brisfknibis/ibis-trackers/Images/drift compensation.png

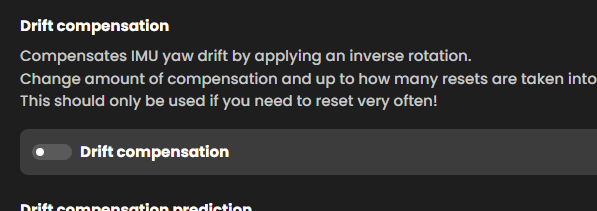
Images/drift compensation.png
