brisfknibis/ibis-trackers/Images/IbisTracker.jpg

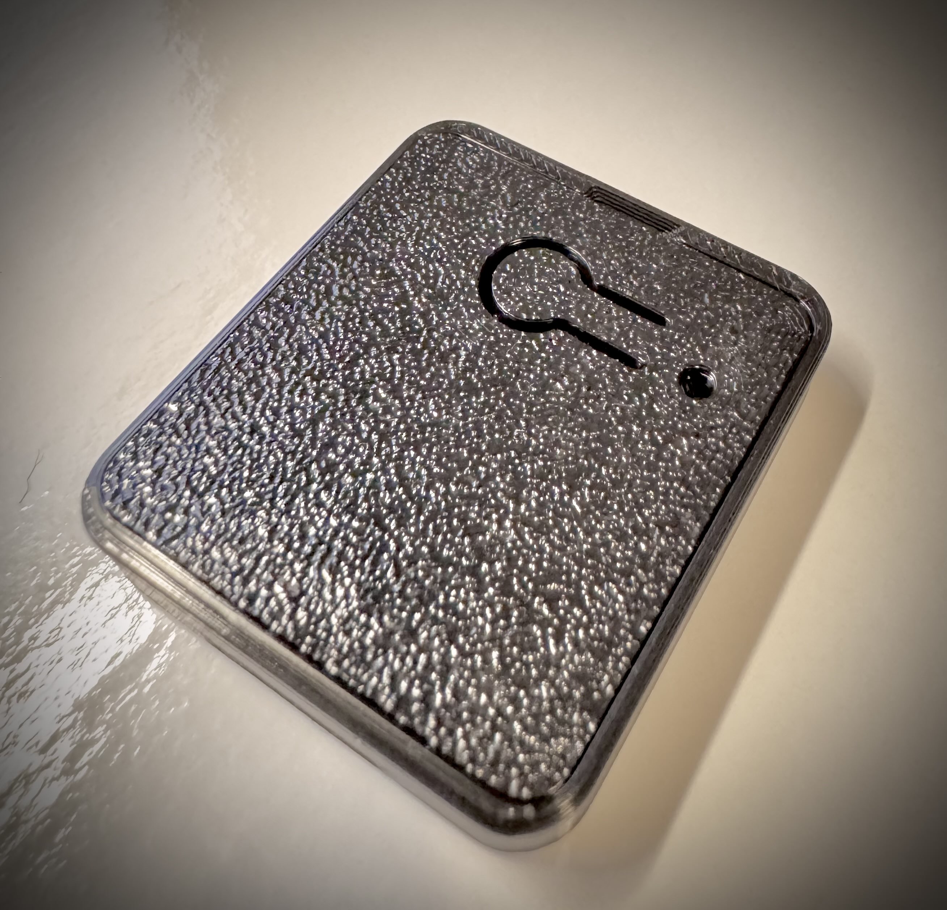
Images/IbisTracker.jpg
