brisfknibis/ibis-trackers/Images/image.png

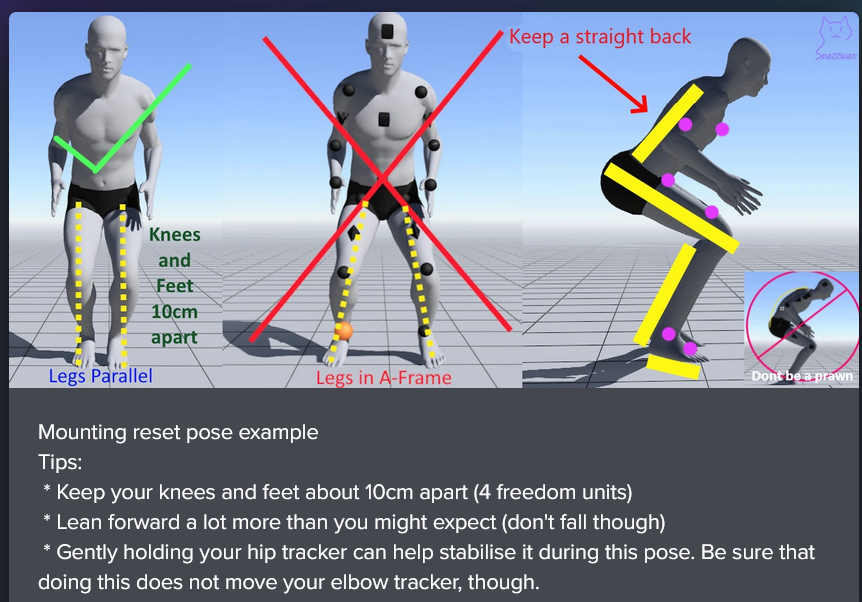
Images/image.png
