brisfknibis/ibis-trackers/Images/IMG_1489.png

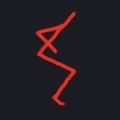
Images/IMG_1489.png
