brisfknibis/ibis-trackers/Images/IMG_7383.png

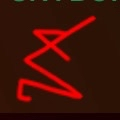
Images/IMG_7383.png
