brisfknibis/ibis-trackers/Images/process/31-mm-wire-antenna.jpg

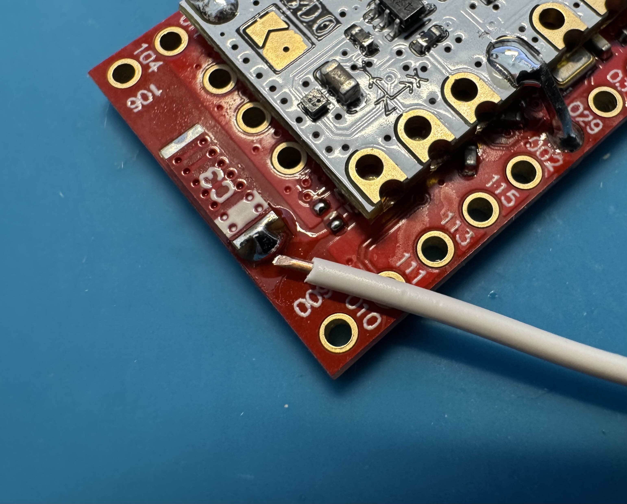
Images/process/31-mm-wire-antenna.jpg
