brisfknibis/ibis-trackers/Images/process/31mm-wire-2.jpg

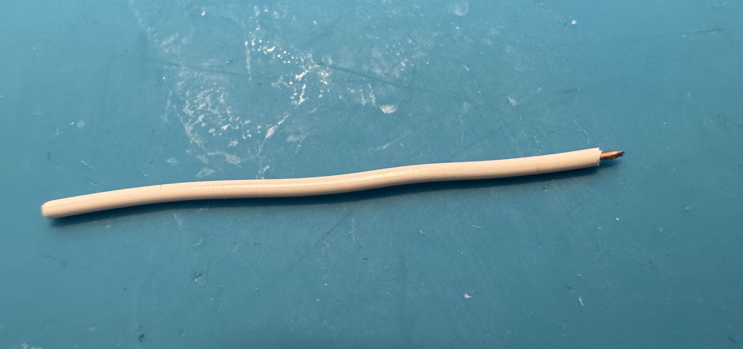
Images/process/31mm-wire-2.jpg
