brisfknibis/ibis-trackers/Images/process/31mm-wire.jpg

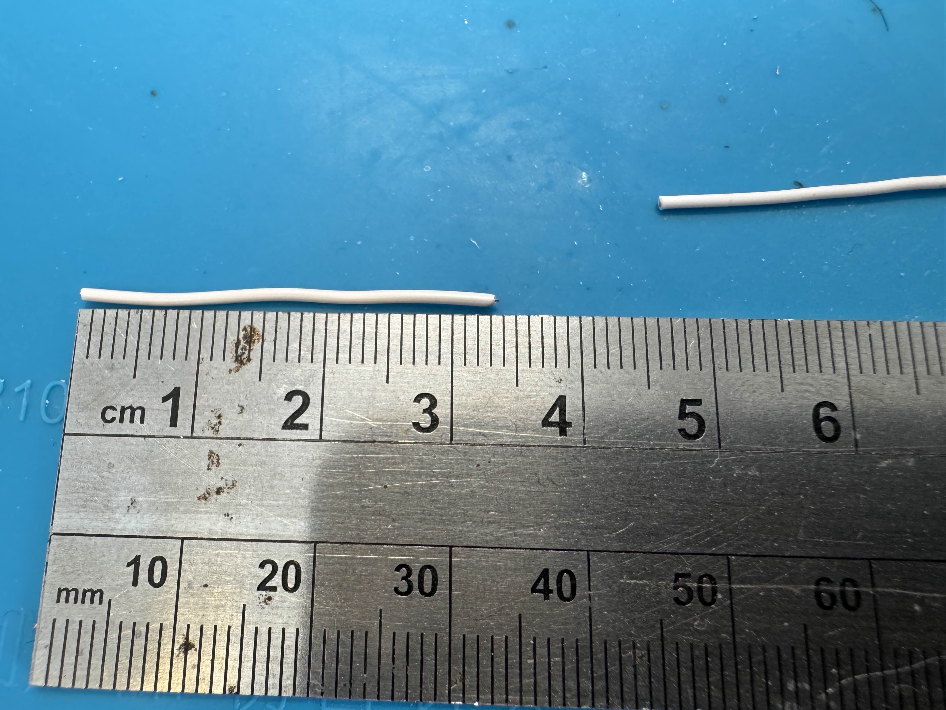
Images/process/31mm-wire.jpg
