brisfknibis/ibis-trackers/Images/process/battery-placement.jpg

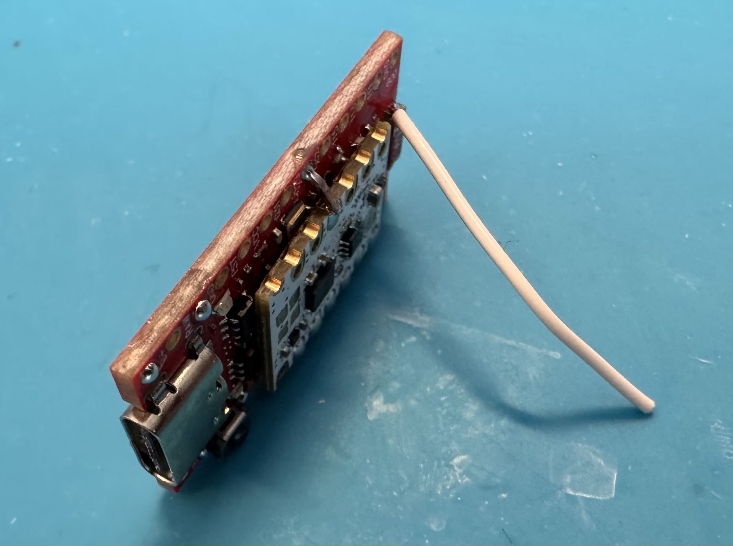
Images/process/battery-placement.jpg
