brisfknibis/ibis-trackers/Images/process/completed-tracker.jpg

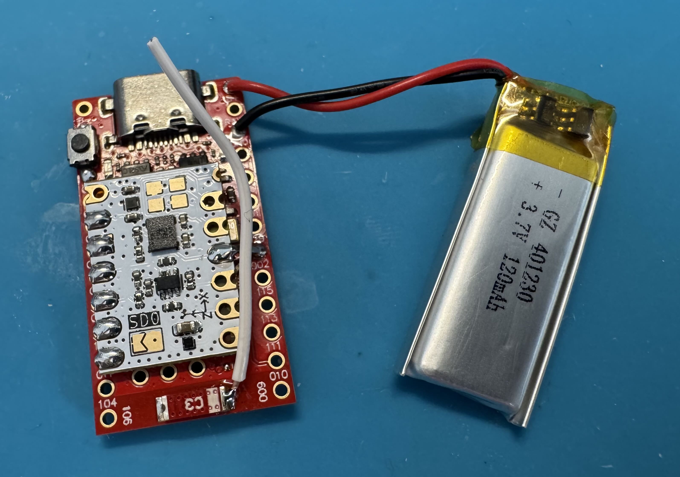
Images/process/completed-tracker.jpg
