brisfknibis/ibis-trackers/Images/process/imu-cube.jpg

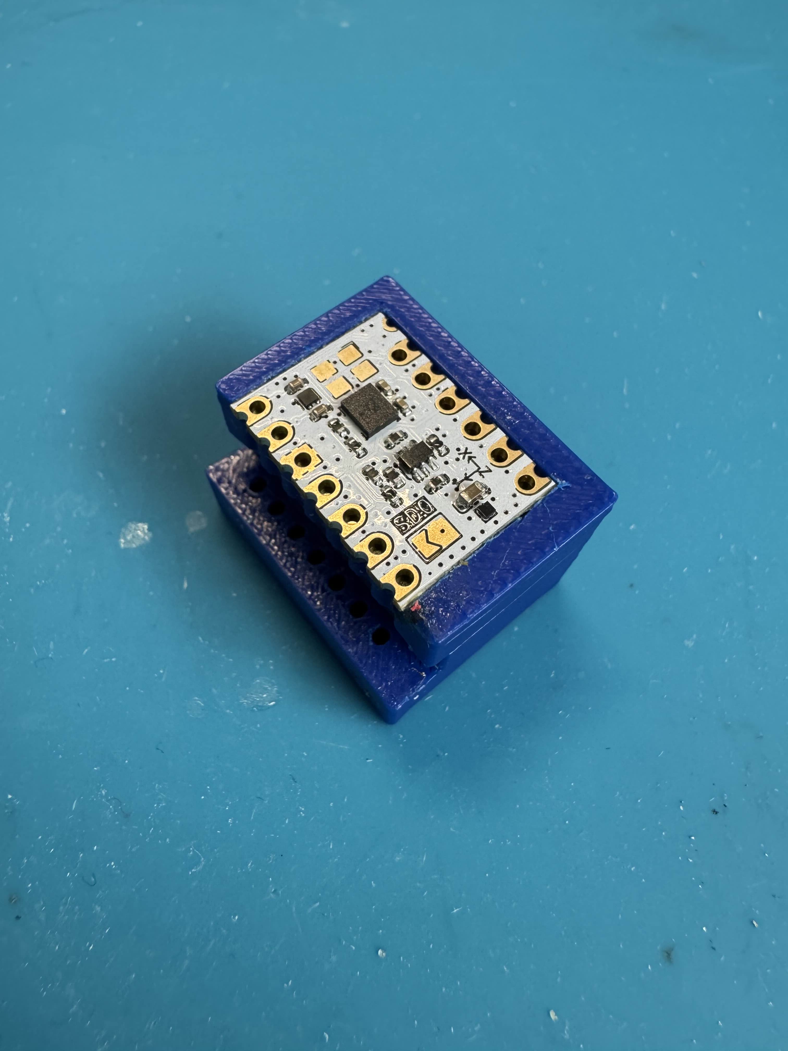
Images/process/imu-cube.jpg
