brisfknibis/ibis-trackers/Images/process/imu-pre-prep.jpg

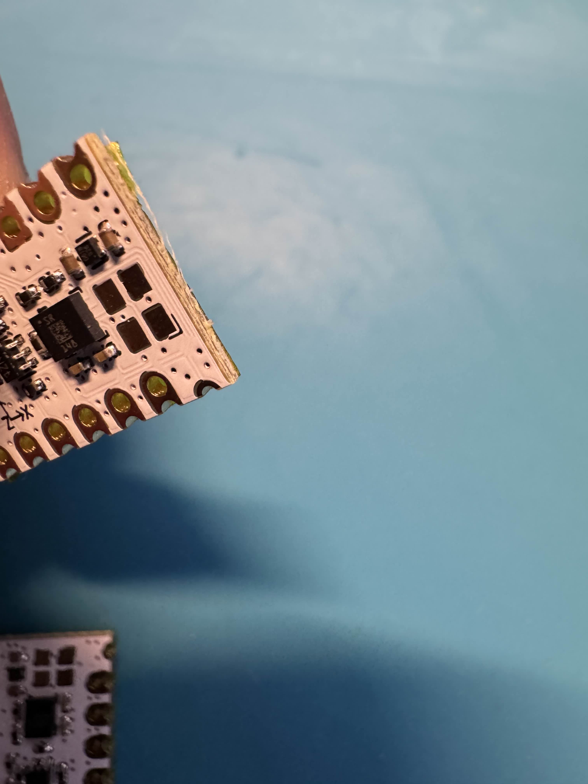
Images/process/imu-pre-prep.jpg
