brisfknibis/ibis-trackers/Images/process/imus-back.jpg

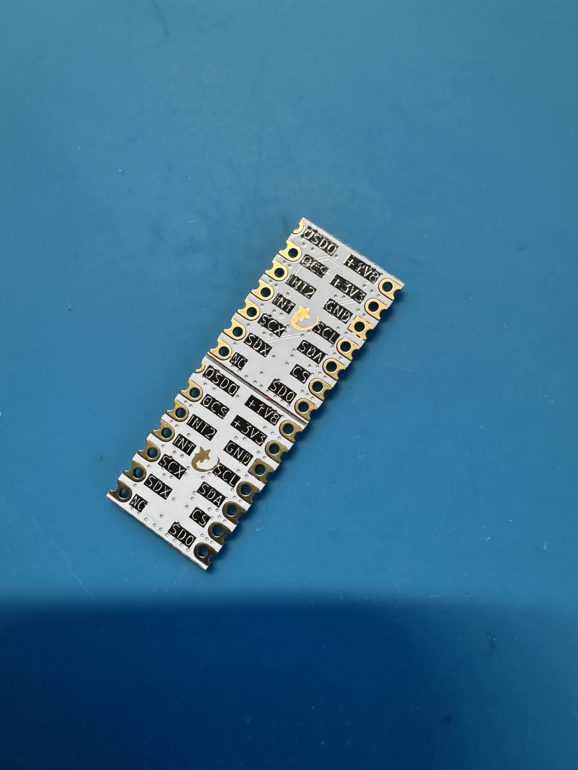
Images/process/imus-back.jpg
