brisfknibis/ibis-trackers/Images/process/imus-front.jpg

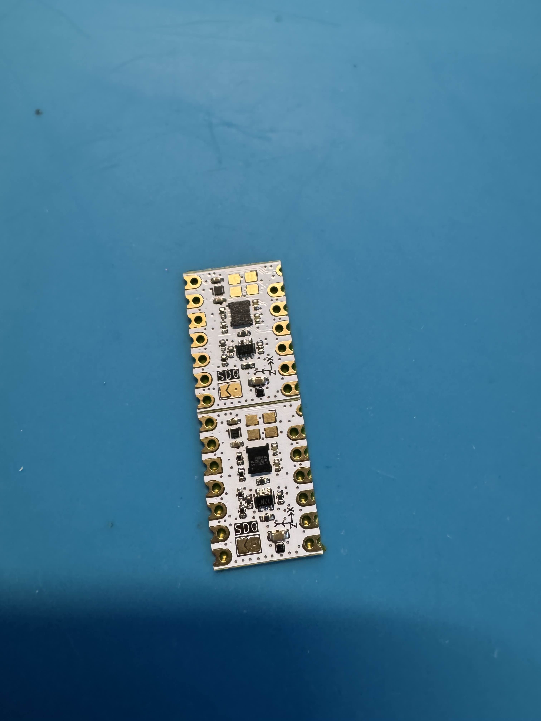
Images/process/imus-front.jpg
