brisfknibis/ibis-trackers/Images/process/serial-termainl-slimenrf-tracker.png

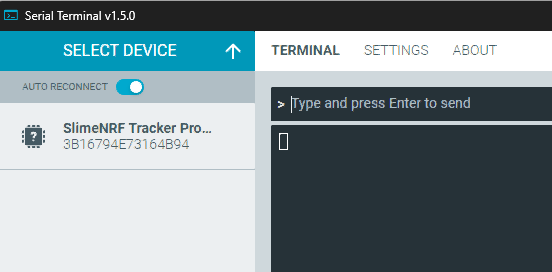
Images/process/serial-termainl-slimenrf-tracker.png
