brisfknibis/ibis-trackers/Images/process/serial-terminal-connect.png

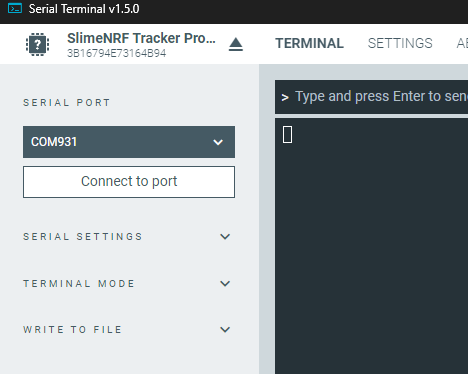
Images/process/serial-terminal-connect.png
