brisfknibis/ibis-trackers/Images/process/serial-terminal-feather.png

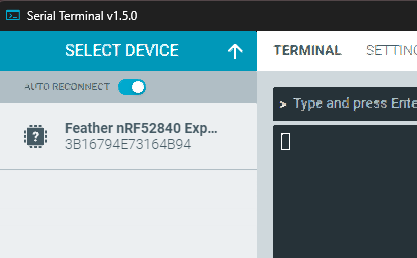
Images/process/serial-terminal-feather.png
