brisfknibis/ibis-trackers/Images/process/serial-terminal-info-screen.png

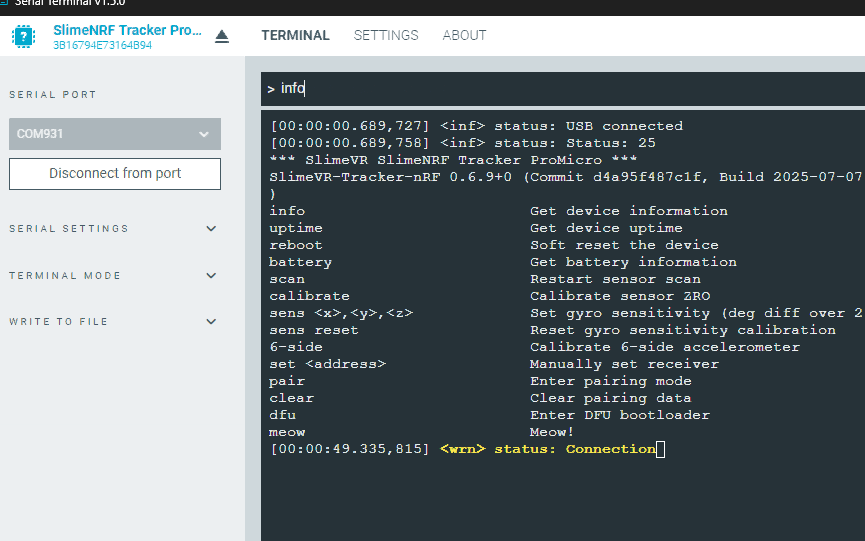
Images/process/serial-terminal-info-screen.png
