brisfknibis/ibis-trackers/Images/process/serial-terminal-info-with-imu.png

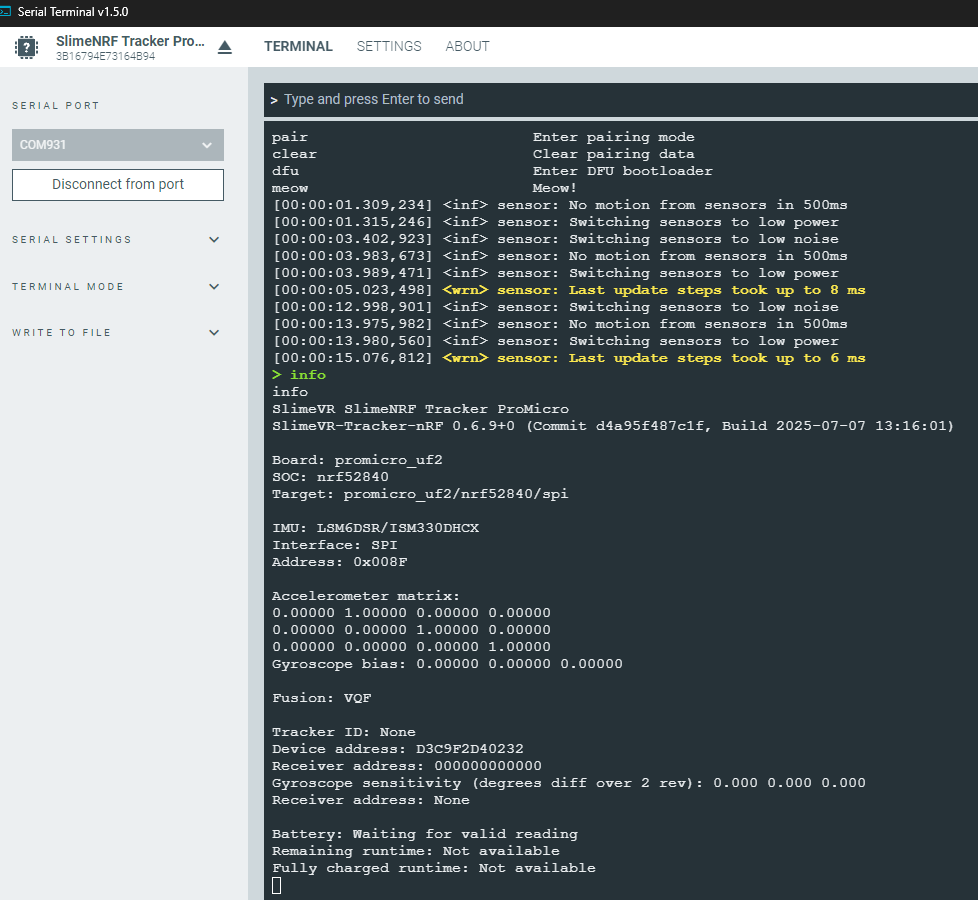
Images/process/serial-terminal-info-with-imu.png
