brisfknibis/ibis-trackers/Images/process/serial-terminal-info.png

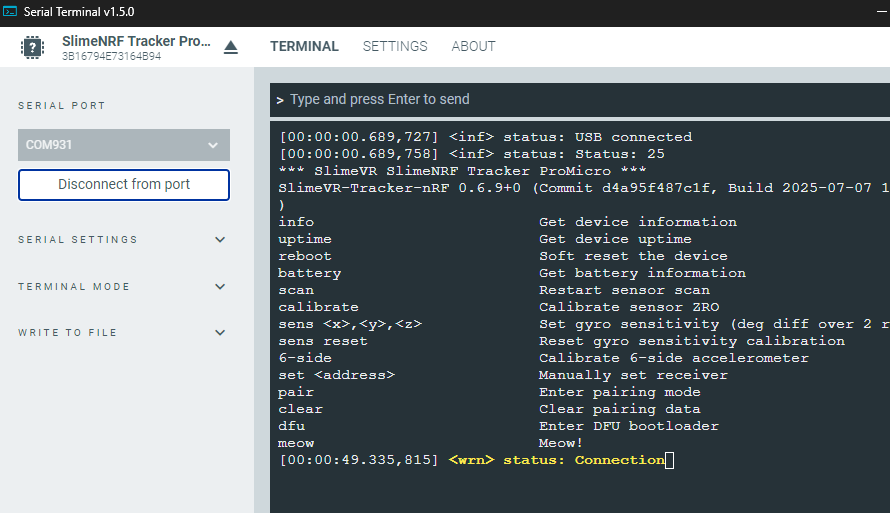
Images/process/serial-terminal-info.png
