brisfknibis/ibis-trackers/Images/process/serial-terminal-nicenano.png

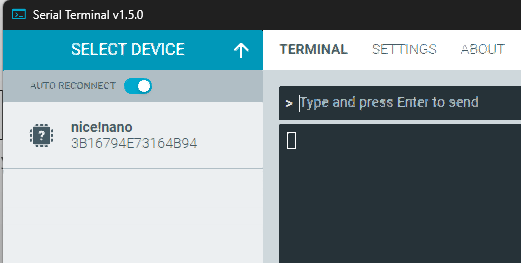
Images/process/serial-terminal-nicenano.png
