brisfknibis/ibis-trackers/Images/process/supermini-back-pins-cut.jpg

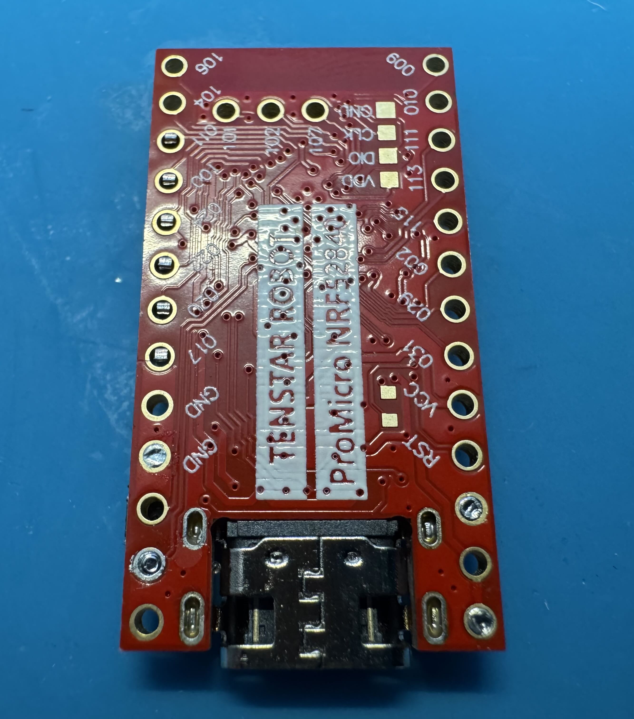
Images/process/supermini-back-pins-cut.jpg
