brisfknibis/ibis-trackers/Images/process/supermini-button.jpg

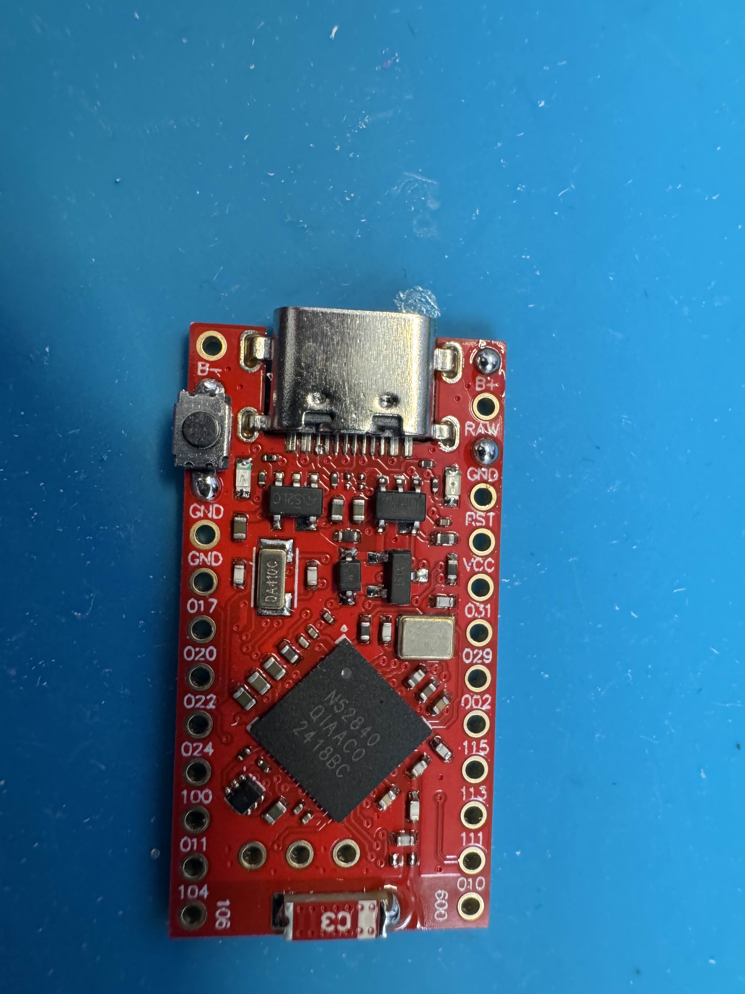
Images/process/supermini-button.jpg
