brisfknibis/ibis-trackers/Images/process/supermini-imu-side-pin-circled.jpg

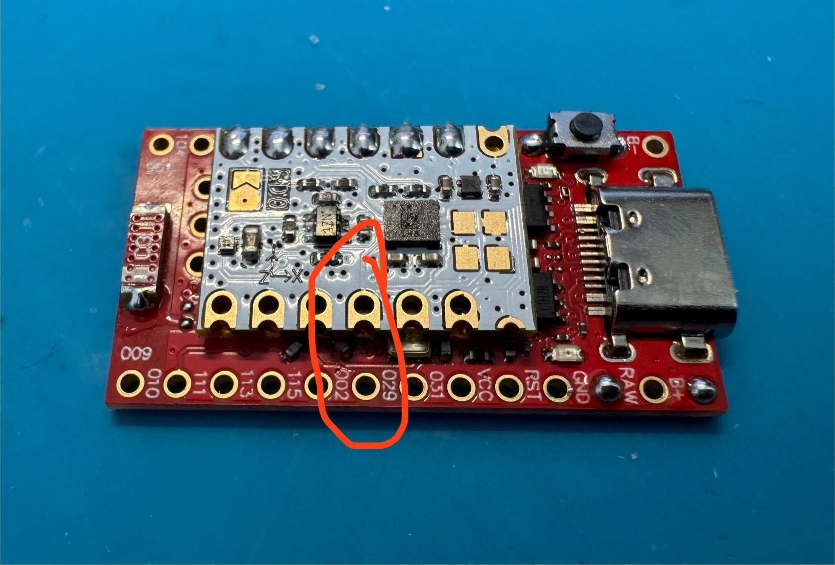
Images/process/supermini-imu-side-pin-circled.jpg
