brisfknibis/ibis-trackers/Images/process/supermini-pin-sodlered-2.jpg

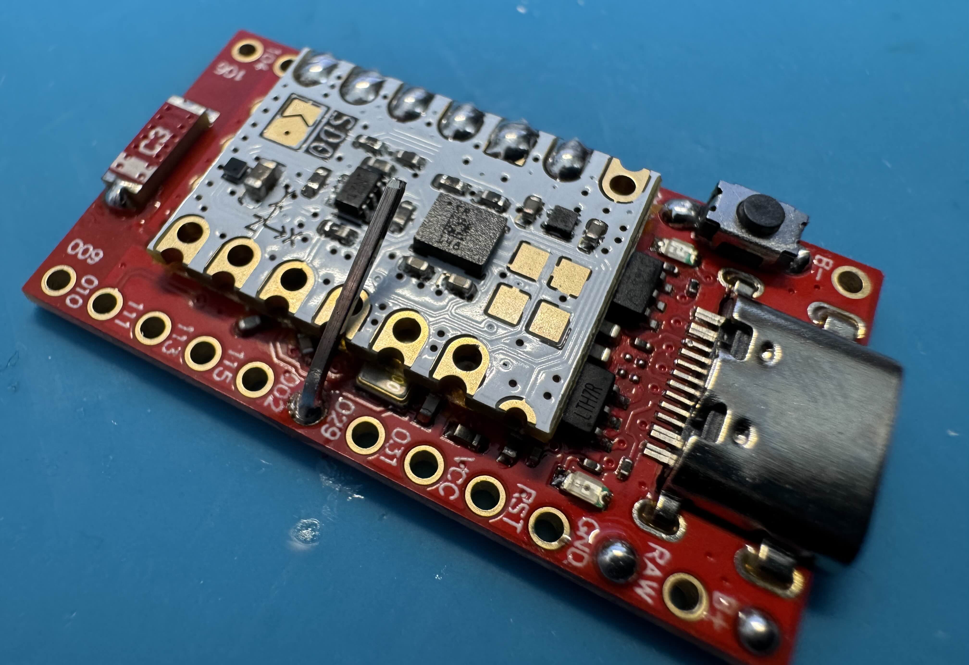
Images/process/supermini-pin-sodlered-2.jpg
