brisfknibis/ibis-trackers/Images/process/supermini-pins-back.jpg

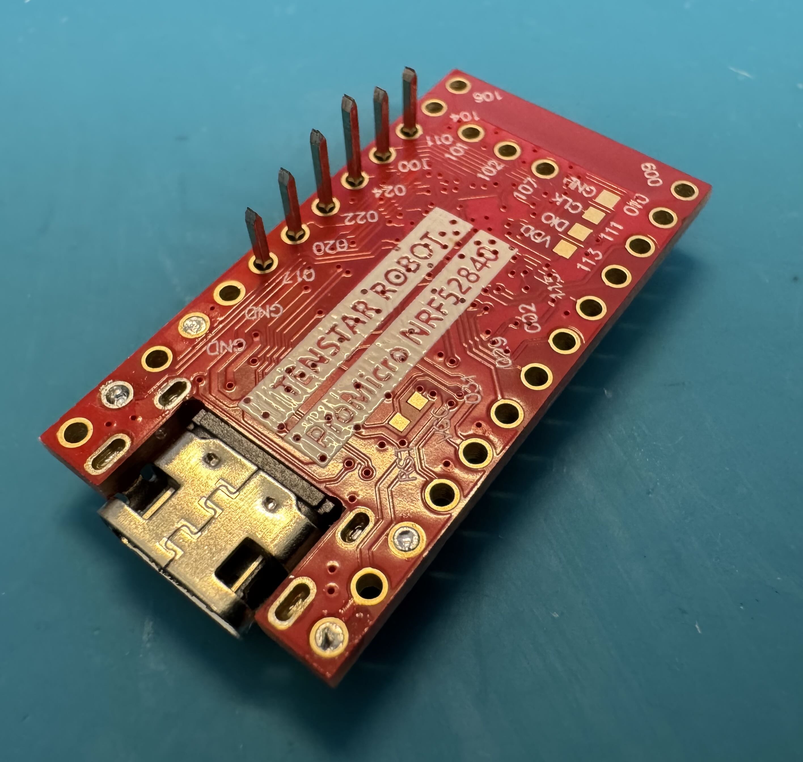
Images/process/supermini-pins-back.jpg
