brisfknibis/ibis-trackers/Images/process/supermini-pins-setting.jpg

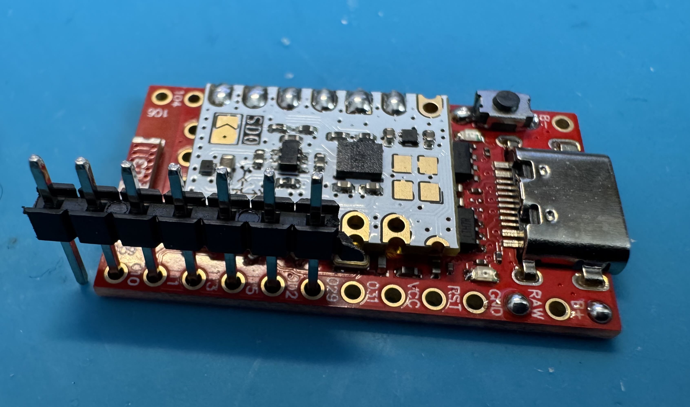
Images/process/supermini-pins-setting.jpg
