brisfknibis/ibis-trackers/Images/process/supermini-prepped-2.jpg

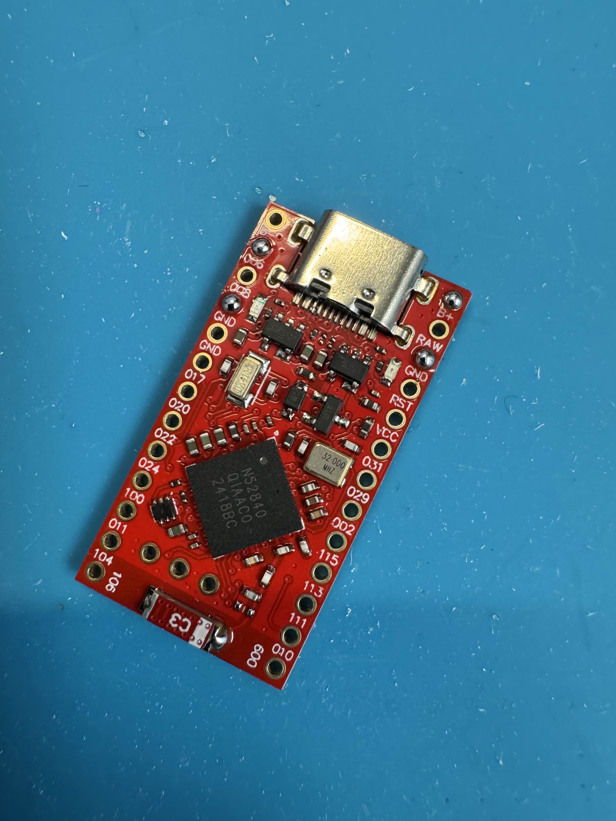
Images/process/supermini-prepped-2.jpg
