brisfknibis/ibis-trackers/Images/process/two-imus-back-kapton-tape.jpg

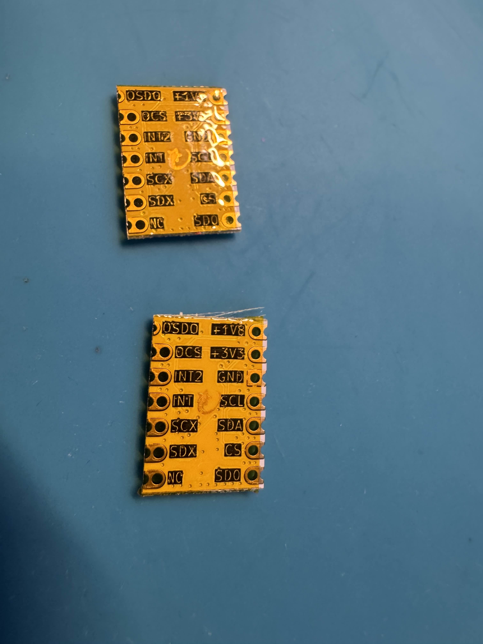
Images/process/two-imus-back-kapton-tape.jpg
