brisfknibis/ibis-trackers/Images/process/two-imus-front.jpg

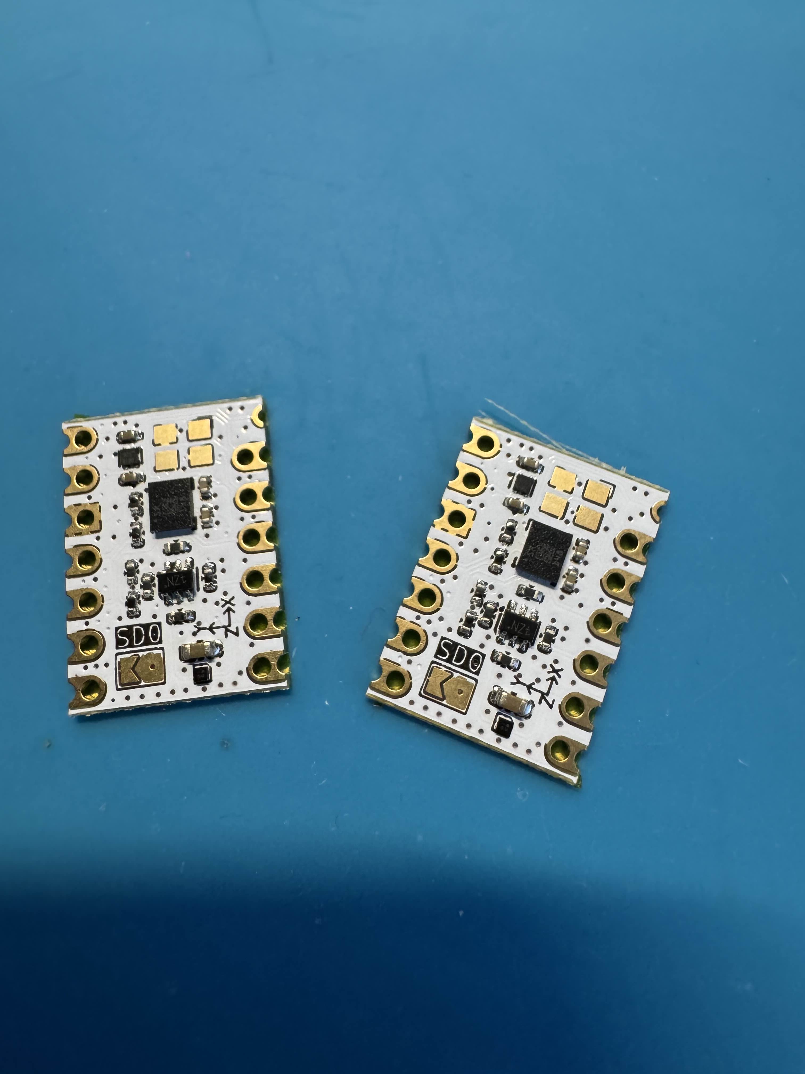
Images/process/two-imus-front.jpg
