brisfknibis/ibis-trackers/Images/R1UvIl8.png

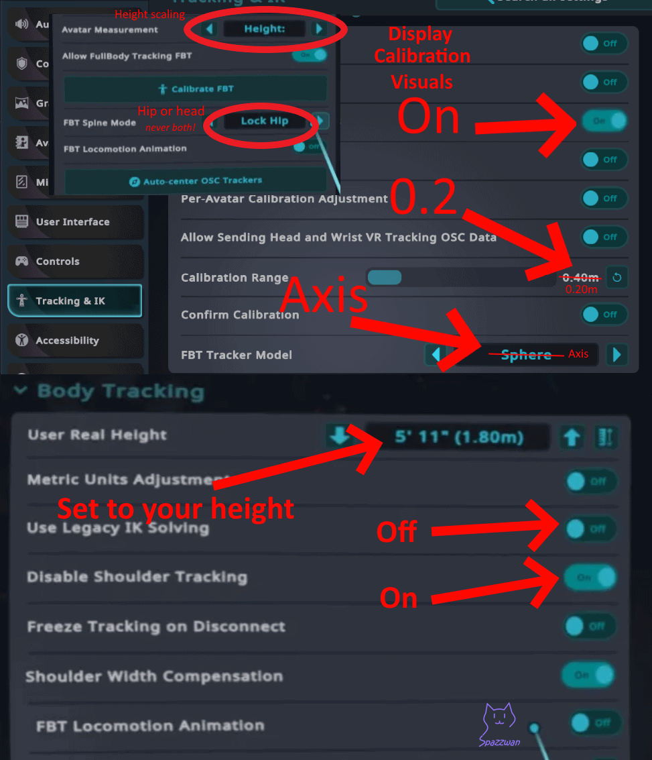
Images/R1UvIl8.png
