brisfknibis/ibis-trackers/Images/smoothing.png

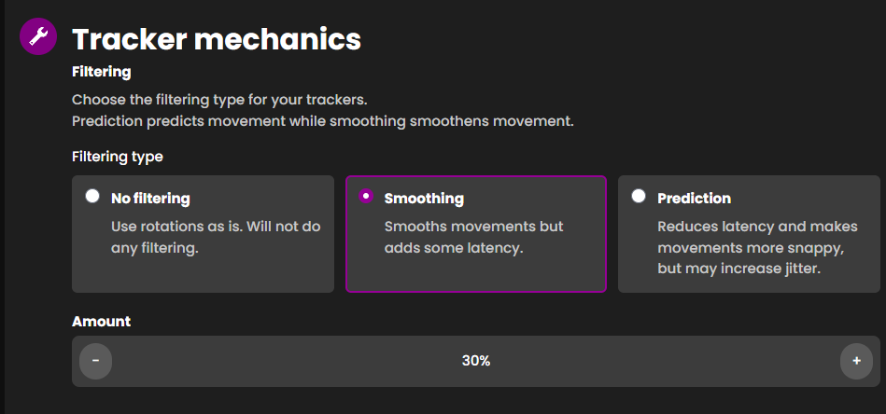
Images/smoothing.png
