brisfknibis/ibis-trackers/Images/tracking settings.png

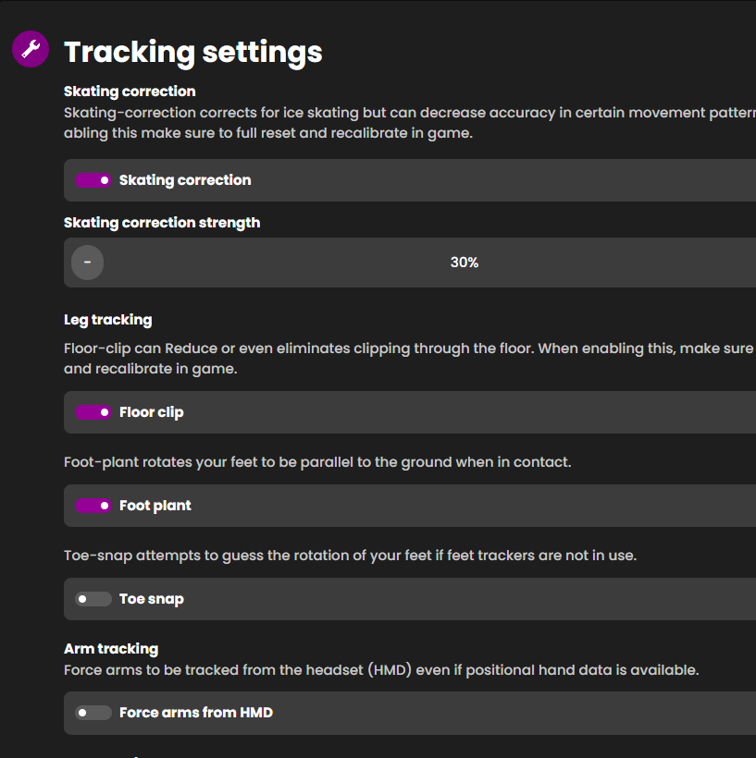
Images/tracking settings.png
