brisfknibis/ibis-trackers/Images/process/raw components.jpg

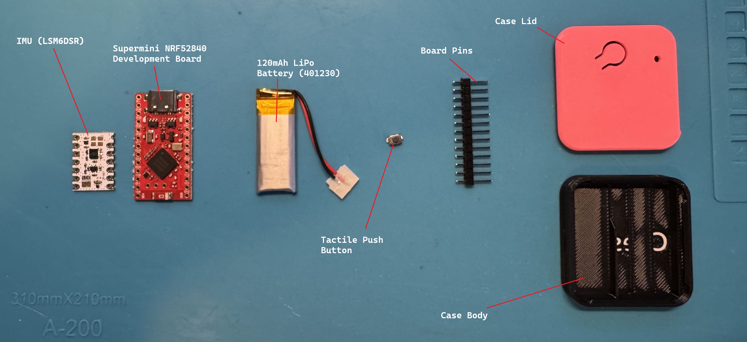
Images/process/raw components.jpg
