brisfknibis/ibis-trackers/3D Print Models/30mm Grippy Hook.stl

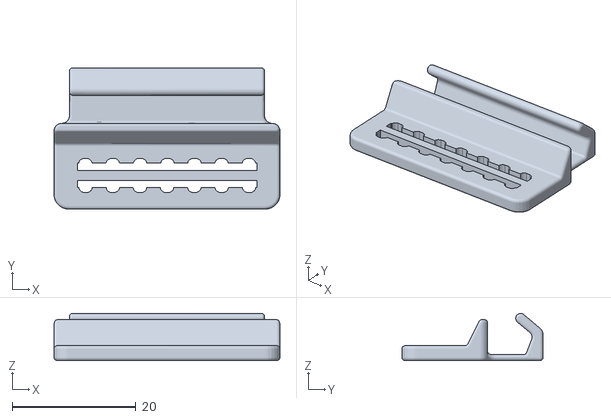
[picture p49: CAD file, 2025-06-15]
3D Print Models/30mm Grippy Hook.stl
36.5 x 22.8 x 7.61
