brisfknibis/ibis-trackers/3D Print Models/38mm Grippy Eyelet.stl

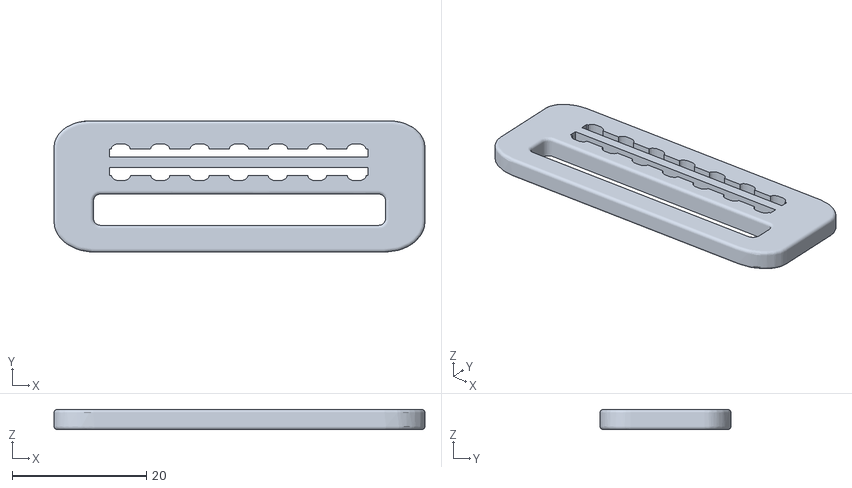
[picture p50: CAD file, 2025-06-15]
3D Print Models/38mm Grippy Eyelet.stl
55.2 x 19.5 x 3.01
