brisfknibis/ibis-trackers/3D Print Models/38mm Grippy Hook.stl

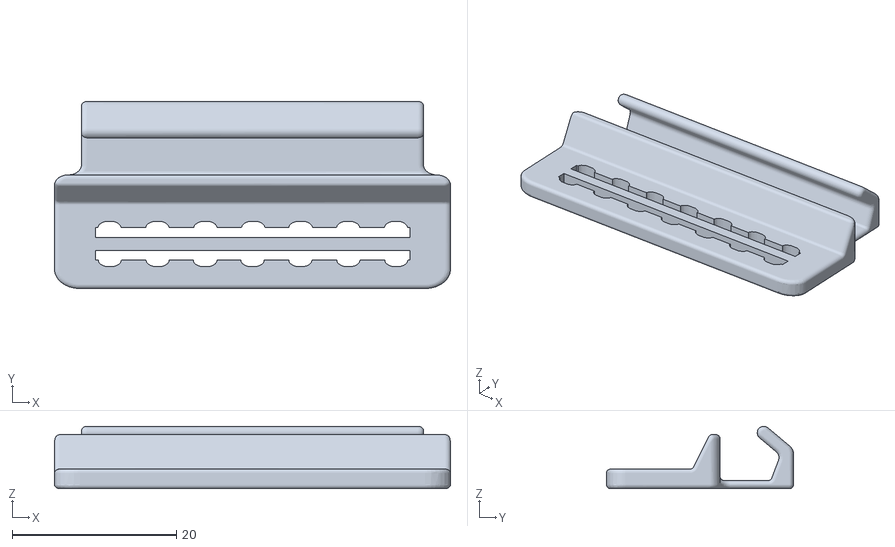
[picture p51: CAD file, 2025-06-15]
3D Print Models/38mm Grippy Hook.stl
48.3 x 22.8 x 7.61
