brisfknibis/ibis-trackers/3D Print Models/30mm Hook.stl

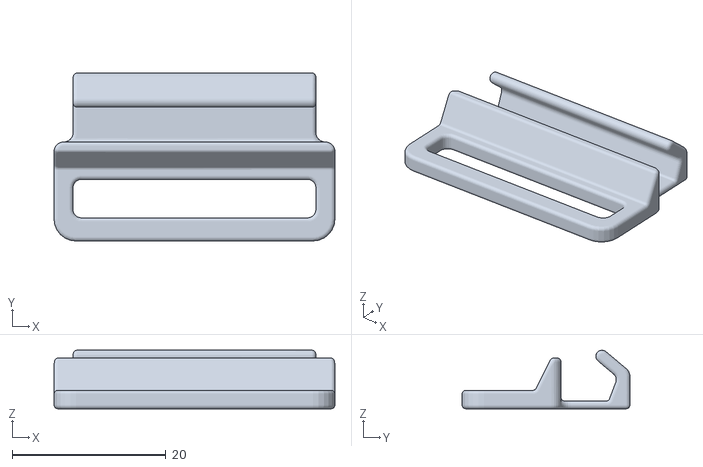
[picture p52: CAD file, 2025-06-15]
3D Print Models/30mm Hook.stl
36.5 x 21.8 x 7.61
