brisfknibis/ibis-trackers/3D Print Models/GoPro Chest Mount.stl

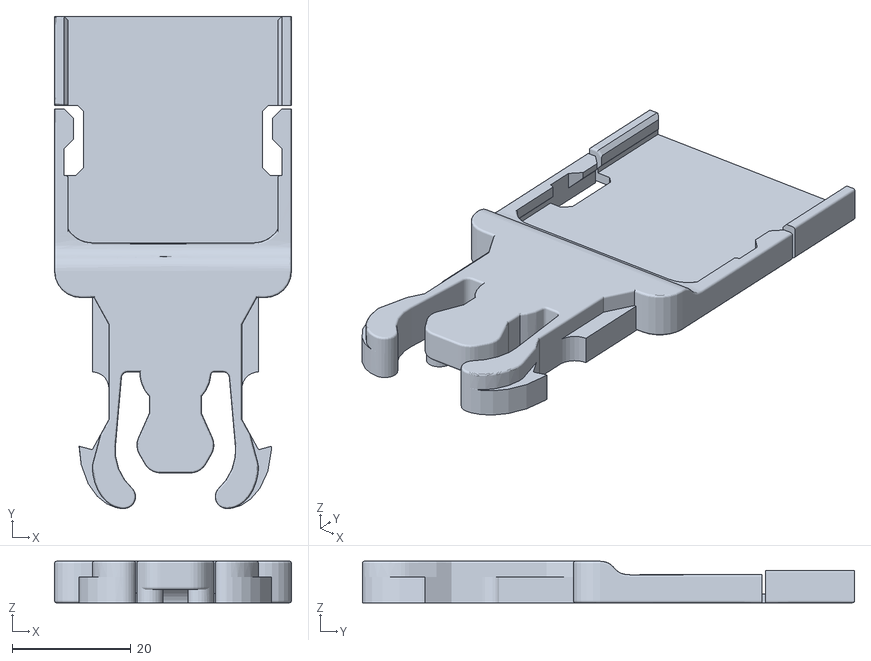
[picture p53: CAD file, 2025-04-01]
3D Print Models/GoPro Chest Mount.stl
39.9 x 82.9 x 7.00
