brisfknibis/ibis-trackers/3D Print Models/30mm Grippy Dovetail.stl

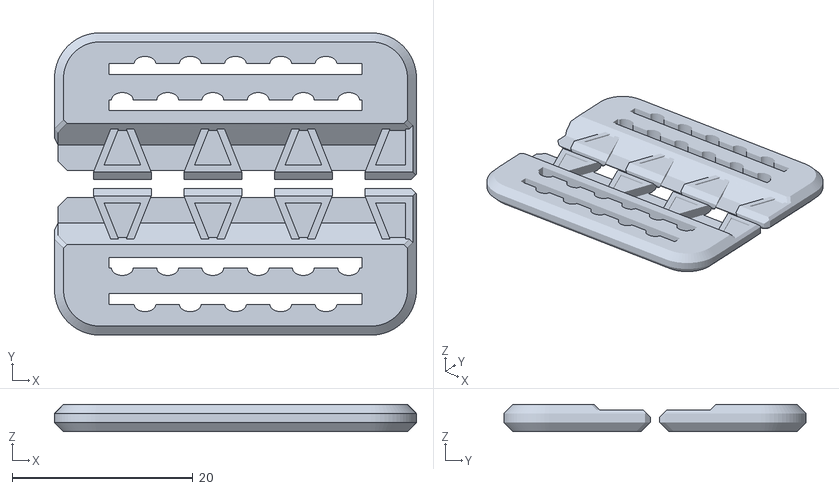
[picture p54: CAD file, 2025-03-08]
3D Print Models/30mm Grippy Dovetail.stl
40.0 x 33.4 x 3.00
