brisfknibis/ibis-trackers/Images/ezgif.com-animated-gif-maker_1.gif

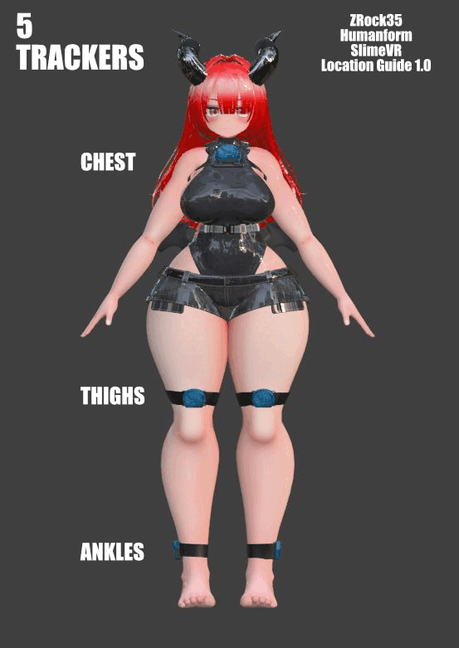
Images/ezgif.com-animated-gif-maker_1.gif
