brisfknibis/ibis-trackers/Images/process/31mm-wire-soldered.jpg

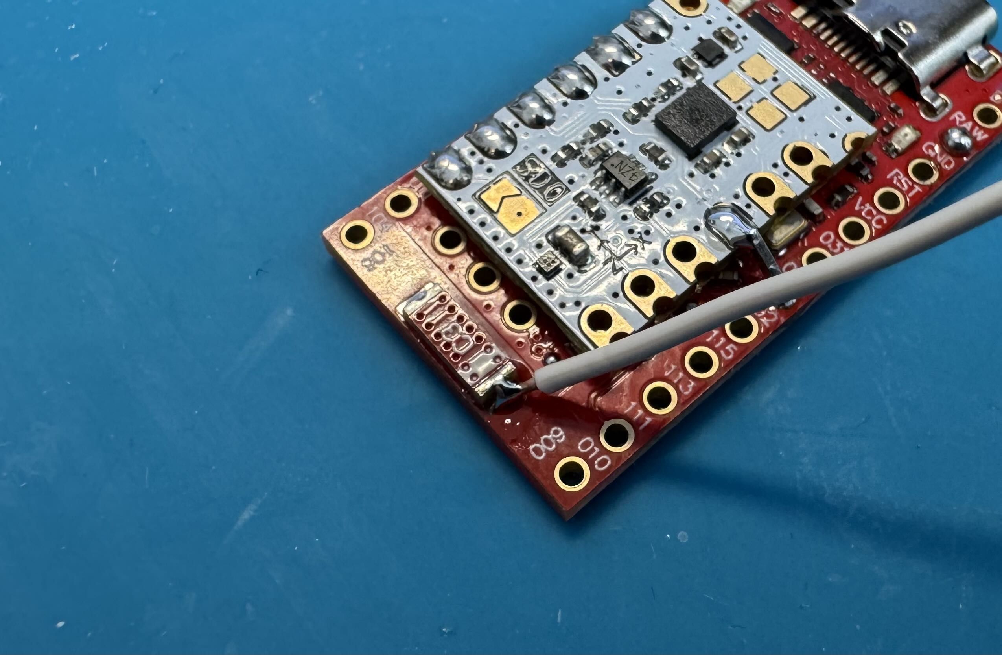
Images/process/31mm-wire-soldered.jpg
