brisfknibis/ibis-trackers/Images/process/imu-soldered-supermini-placement.jpg

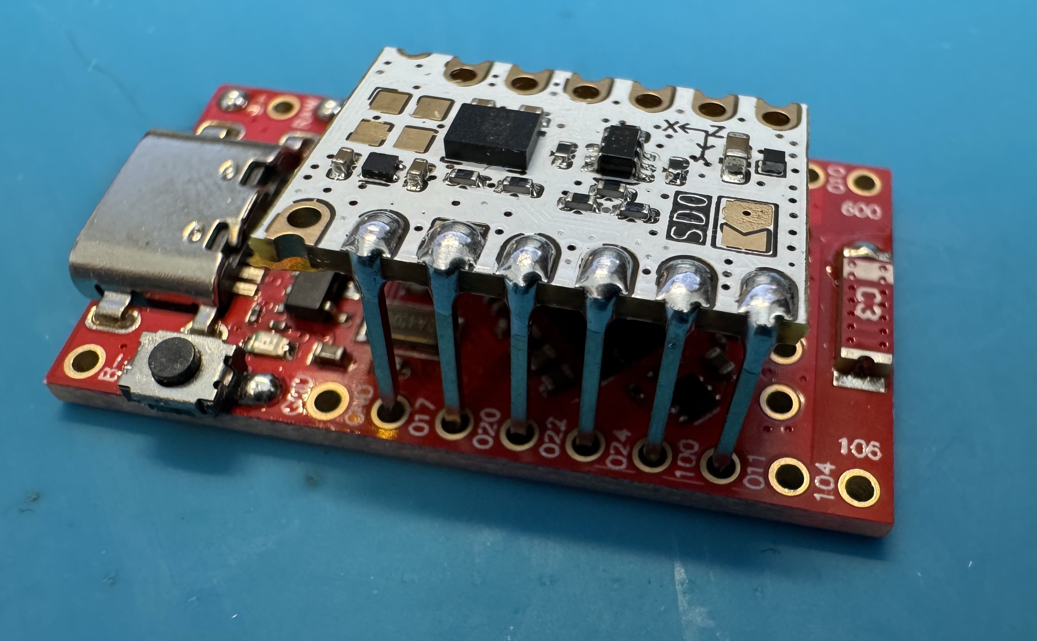
Images/process/imu-soldered-supermini-placement.jpg
