brisfknibis/ibis-trackers/Images/process/soldering-cube-pins.jpg

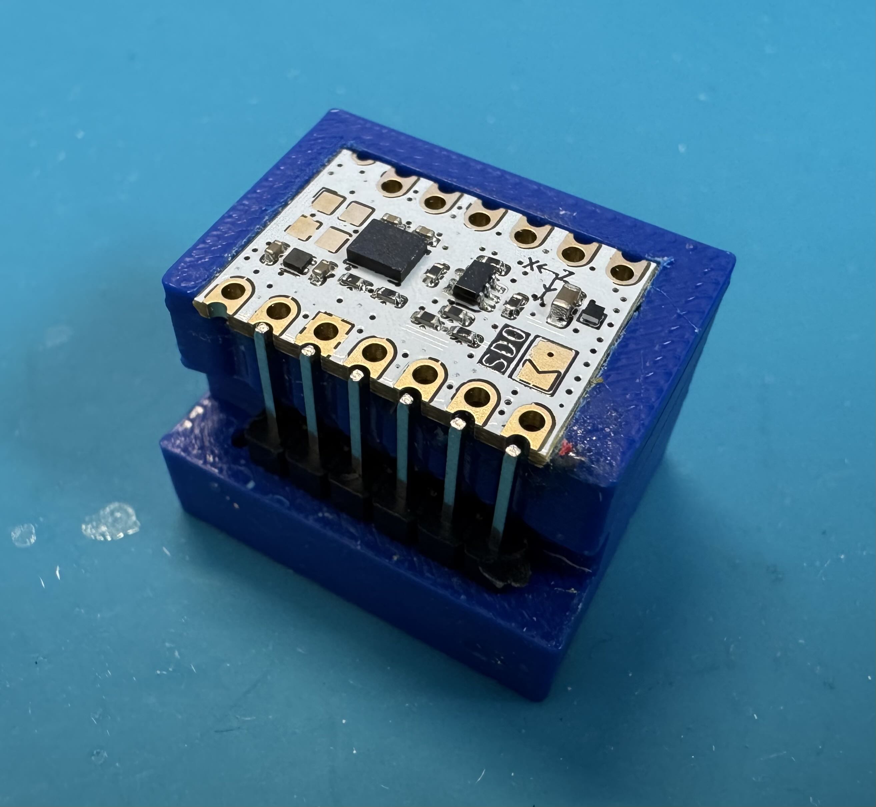
Images/process/soldering-cube-pins.jpg
