brisfknibis/ibis-trackers/Images/process/supermini-pins-set-soldered.jpg

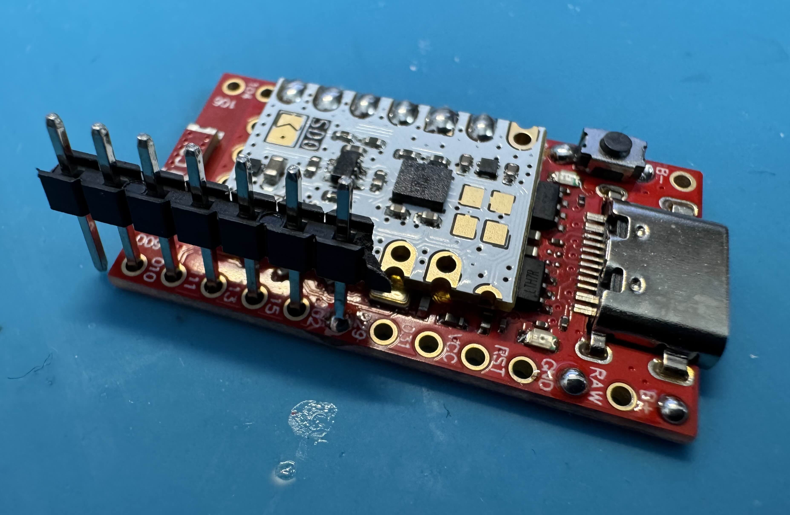
Images/process/supermini-pins-set-soldered.jpg
