brisfknibis/ibis-trackers/Images/process/supermini-pins-soldered.jpg

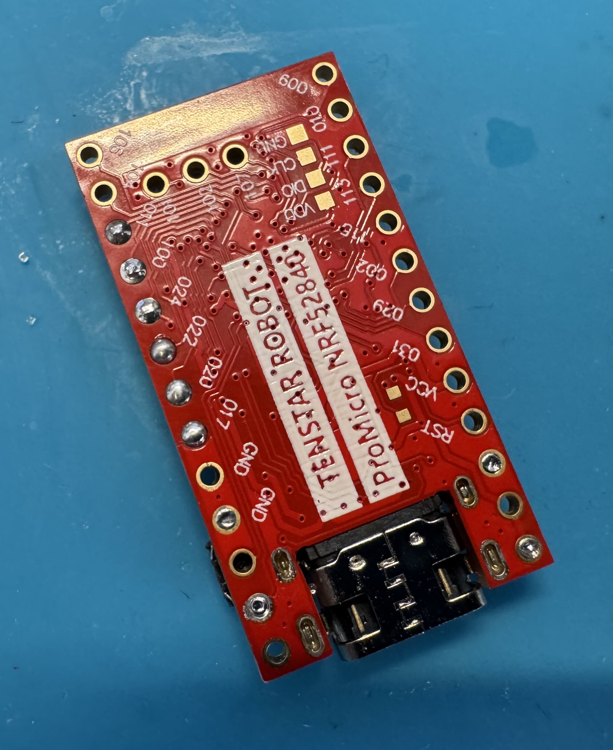
Images/process/supermini-pins-soldered.jpg
